siteswapjuggler/meuhcube/software/arduino/cubeled_v1.3/todo_list.ino

/*
   LISTE DE PISTES D'AMELIORATIONS

   Il faut que j'implémente l'interframe.
   mettre le parser en classe pour permettre l'envoi via de multiples port série
   emmettre une synchro externe (logicielle et matérielle)

   SET_CUBE avec moins de paramètre et propagation (line qui se répète ou plan qui se répète)

   A FAIRE COTE ORDI :

   AND, OR, XOR... opérations binaires sur l'ensemble du cube (pour compléter les reverse en fait) non tout ça doit être fait coté PC
   MOVE&COPY...    idem tout ça doit être fait coté PC

   NOTE pour les plans il faudrait aussi les inverses (plan en passant de l'autre coté du cube
   DES COMMANDES QUI STACKENT L'INFO (historique de l'info), genre une ligne mais chauqe nouvelle ligne décalle la ligne précédente (pour faire de la dataviz faciel
   UNE VARIABLE ANIMATE POUR FAIRE DE L'ANIMATION DIRECTEMENT ET QUI EXECUTE DES COMMANDE D'ANIMATION SIMPLE >> le parser comme objet pour en avoir deux en parallelle
*/
