siteswapjuggler/meuhcube/software/arduino/cubeled_v1.3/version.ino

/*
   v1.3 - ajout du mode Démo
   correction rev_line
   correction rev_pixel
   ajout rev_plan
   phrase de connection changée en "Meuhcube online"
 
   v1.2 - bcp d'améliorations
   gestion paramètres en eeprom
   ajout de la commande plan
   ajout de la commande mouvement et modulo

   v1.1 - complément de commandes
   nouvelles commandes

   v1   - release d'origine
   commandes de bases

*/
